Sanugiw/Dual-Mode-Thermometer/Temperature sesnsor.asc

C1: cap; 1µ; V=6.3 Irms=0 Rser=0.0122 Lser=339p mfg="Würth Elektronik" pn="885012105006 WCAP-CSGP 0402" type="X5R"
C2: cap; 1µ; V=6.3 Irms=0 Rser=0.0122 Lser=339p mfg="Würth Elektronik" pn="885012105006 WCAP-CSGP 0402" type="X5R"
C3: cap; 1µ
C4: cap; 1µ
C5: cap; 10µ
C6: cap; 680µ
C7: cap; 0.1µ
C8: cap; 1000µ
C9: cap; 1000µ
D1: zener; BZX84C12L
D2: diode; 1N914
D3: diode; 1N914
D7: zener; BZX84C24VLY
D13: zener; STZ5_6N
L1: ind2; 2.2
L2: ind2; 4.8m
PT: res; 157.325
Q1: npn
R1: res; 10K; tol=1 pwr=0.1
R2: res; 10K; tol=1 pwr=0.1
R3: res; 10K; tol=1 pwr=0.1
R4: res; 1k; tol=1 pwr=0.1
R5: res; 1k
R6: res; 10k
R7: res; 10k
R8: res; 10k
R9: res; 10k
R10: res; 10k
R11: res; 10k
R12: res; 6.6k
R13: res; 100
R14: res; 100
R15: res; 10
R16: res; 100
R17: res; 1k
R18: res; 1k
R19: res; 470
R20: res; 10
R21: res; 50
R22: res; 10k
R23: res; {R}
R24: res; 50
R25: res; 5k
R26: res; 2k
R27: res; 180
U1: AD744
U2: AD744
U3: AD744
V2: signal; SINE(0 325 50)
Named nets: 0
at 25 C R is 10k
at 50 C R is about 3.6 k
at -20 R is 92.160 ohms.
at 150 R is 157.325 ohms
K L1 L2 1
.tran 10
.step param R 4k 10k 1k
